Mjrovai/ArduFarmBot-2/ArduFarmBot2_PartialTest/ArduFarmBot2_PartialTest.ino

/***************************************************************************************************************
 * IoT DHT Temp/Hum Station using NodeMCU ESP-12 Develop Kit V1.0
 *  DHT connected to NodeMCU pin D3
 *  DHT Data on local OLED Display
 *
 *  Developed by MJRovai 12 October 2017
 ********************************************************************************************************************************/

/* OLED */
#include <ACROBOTIC_SSD1306.h> // library for OLED: SCL ==> D1; SDA ==> D2
#include <SPI.h>
#include <Wire.h>

/* DHT22*/
#include "DHT.h"
#define DHTPIN D3  
#define DHTTYPE DHT22 
DHT dht(DHTPIN, DHTTYPE);
float hum = 0;
float temp = 0;

void setup() 
{
  Serial.begin(115200);
  delay(10);
  dht.begin();
  oledStart();
}

void loop() 
{
  getDhtData();
  displayData();
  delay(2000); // delay for getting DHT22 data
}

/***************************************************
 * Start OLED
 **************************************************/
void oledStart(void)
{
  Wire.begin();  
  oled.init();                      // Initialze SSD1306 OLED display
  clearOledDisplay();
  oled.clearDisplay();              // Clear screen
  oled.setTextXY(0,0);              
  oled.putString("  MJRoBot.org");
}

/***************************************************
 * Get DHT data
 **************************************************/
void getDhtData(void)
{
  float tempIni = temp;
  float humIni = hum;
  temp = dht.readTemperature();
  hum = dht.readHumidity();
  if (isnan(hum) || isnan(temp))   // Check if any reads failed and exit early (to try again).
  {
    Serial.println("Failed to read from DHT sensor!");
    temp = tempIni;
    hum = humIni;
    return;
  }
}

/***************************************************
 * Display data at Serial Monitora & OLED Display
 **************************************************/
void displayData(void)
{
  Serial.print(" Temperature: ");
  Serial.print(temp);
  Serial.print("oC   Humidity: ");
  Serial.print(hum);
  Serial.println("%");
  
  oled.setTextXY(3,0);              // Set cursor position, start of line 2
  oled.putString("TEMP: " + String(temp) + " oC");
  oled.setTextXY(5,0);              // Set cursor position, start of line 2
  oled.putString("HUM:  " + String(hum) + " %");
}

/***************************************************
 * Clear OLED Display
 **************************************************/
void clearOledDisplay()
{
  oled.setFont(font8x8);
  oled.setTextXY(0,0); oled.putString("                ");
  oled.setTextXY(1,0); oled.putString("                ");
  oled.setTextXY(2,0); oled.putString("                ");
  oled.setTextXY(3,0); oled.putString("                ");
  oled.setTextXY(4,0); oled.putString("                ");
  oled.setTextXY(5,0); oled.putString("                ");
  oled.setTextXY(6,0); oled.putString("                ");
  oled.setTextXY(7,0); oled.putString("                ");
  oled.setTextXY(0,0); oled.putString("                ");              
}
